jdp999/dactyl-manuform/things/right.stl

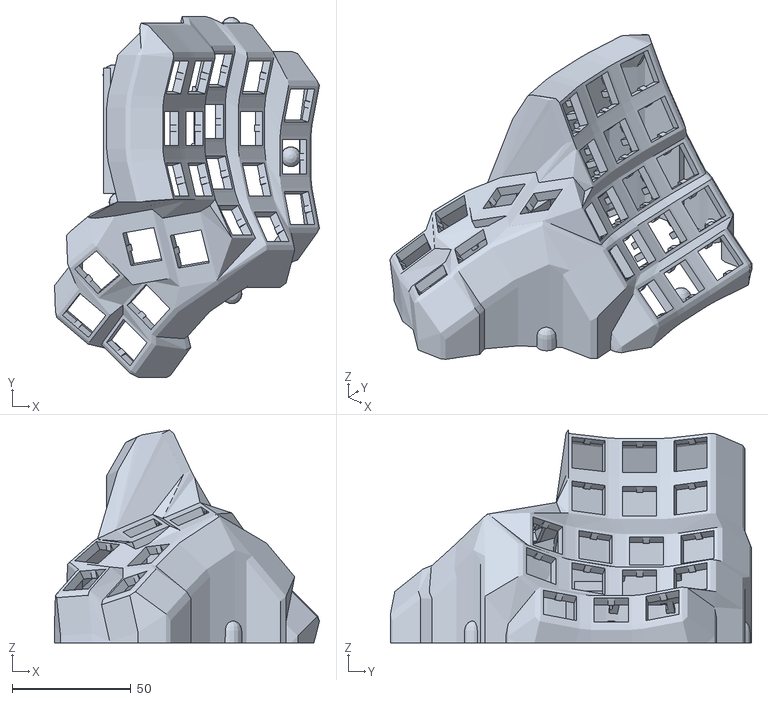
[picture p16: CAD file, 2021-02-27]
things/right.stl
111.8 x 152.3 x 89.8
