jdp999/dactyl-manuform/things/right6x7-MOD1.stl

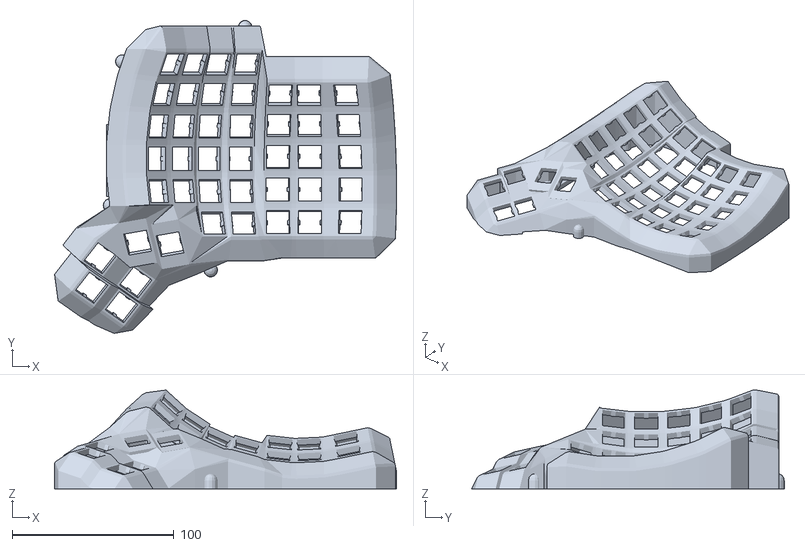
[picture p17: CAD file, 2021-02-27]
things/right6x7-MOD1.stl
211.5 x 193.4 x 61.2
