jdp999/dactyl-manuform/things/right-4x6-plate.dxf

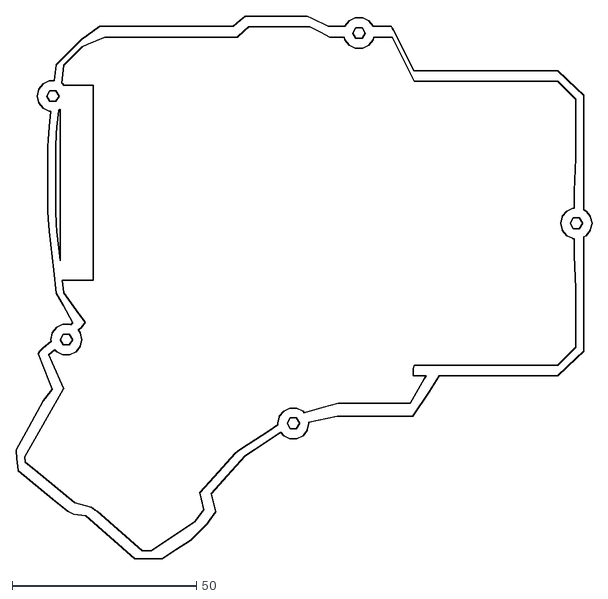
[picture p18: CAD file, 2021-02-27]
things/right-4x6-plate.dxf
156.5 x 147.5
