jdp999/dactyl-manuform/things/right-4x5-plate.dxf

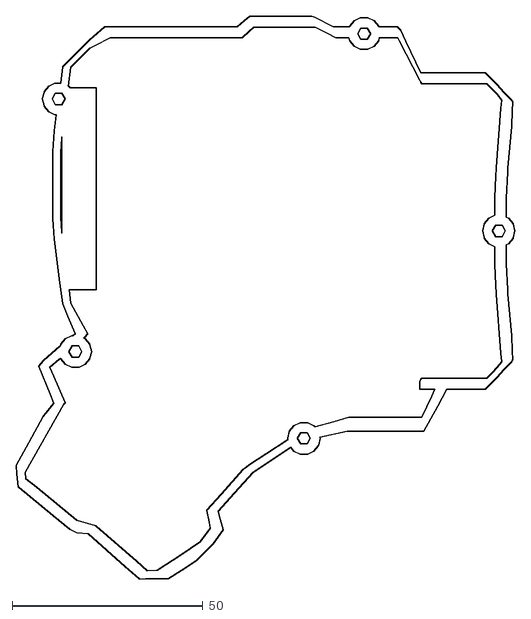
[picture p19: CAD file, 2021-02-27]
things/right-4x5-plate.dxf
130.7 x 147.5
