jdp999/dactyl-manuform/things/right-plate.dxf

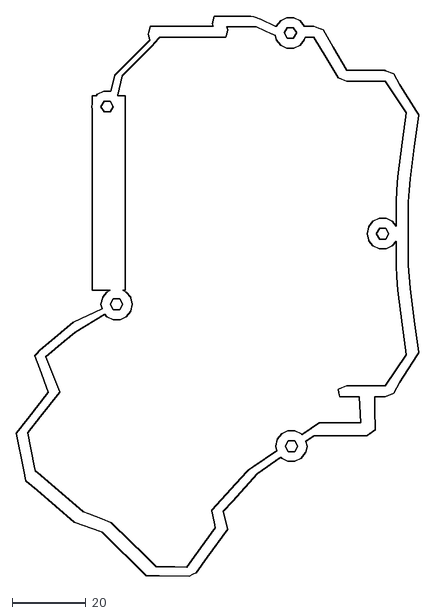
[picture p20: CAD file, 2021-02-27]
things/right-plate.dxf
109.4 x 152.3
